Andymann/esp32-midi-processor/diagrams/03-routing-matrix.png

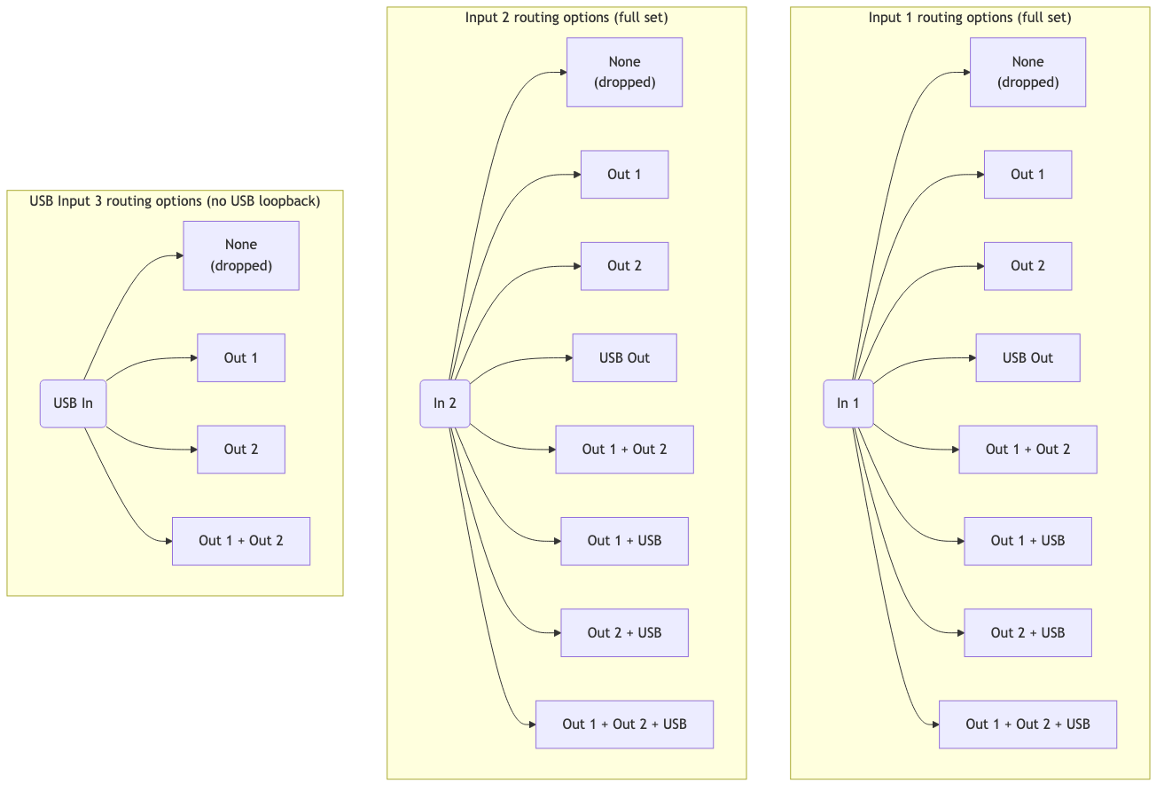
diagrams/03-routing-matrix.png
