Andymann/esp32-midi-processor/diagrams/04-modifier-details.png

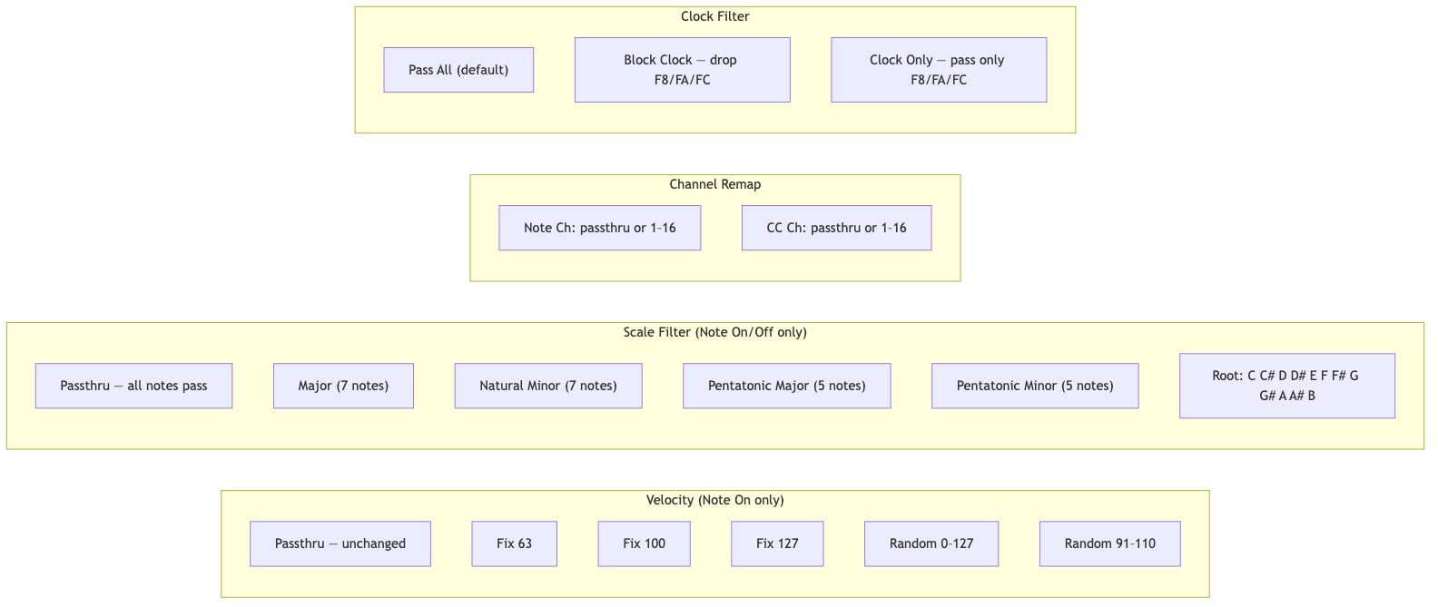
diagrams/04-modifier-details.png
