Andymann/esp32-midi-processor/diagrams/05-queue-sequence.png

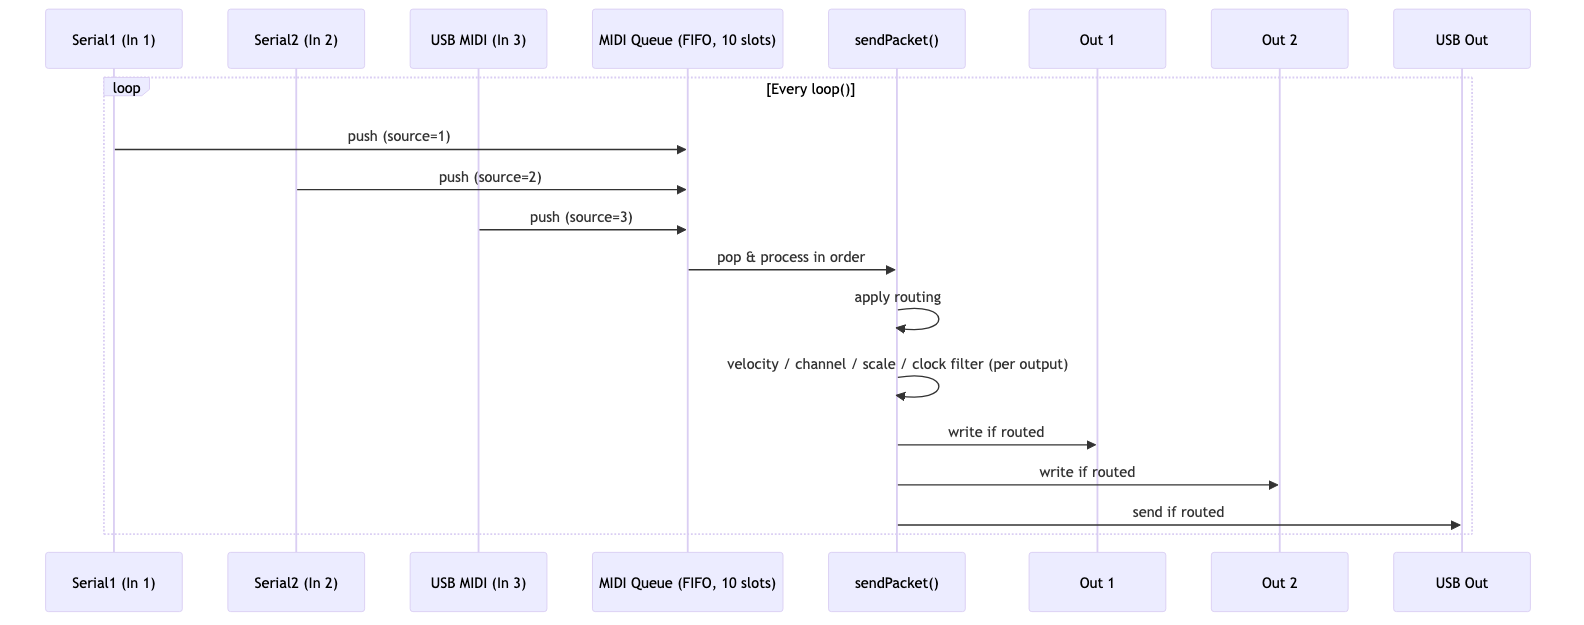
diagrams/05-queue-sequence.png
